mateuszb0k/humanoid-head/vision-module/documentation/training_details.pdf

### Vision Module - Technical Documentation

Mikoªaj Baran, Kewin Kisiel, Szymon Wójcik

March 2026

## Contents

1 Introduction | 3
2 Dataset Composition and Preprocessing | 3
3 Neural Network Architectures and Training | 4

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

## 1 Introduction

The primary objective of this project is the construction of a robotic head capable of two-way communication and emotional expression. The vision system's core responsibility is detecting user faces, extracting landmarks, and identifying aective states across seven categories: anger, sadness, fear, surprise, disgust, happiness, and neutral. The output data is utilized to personalize interactions via the speech synthesis subsystem.

## 2 Dataset Composition and Preprocessing

### 2.1 Data Sources

The training corpus was aggregated from diverse repositories to ensure high variance and reliability. Key sources included:

| Public Repositories: Aggregated versions of FER-2013, RAF-DB, and AectNet datasets.
| Synthetic Data: Images generated using the Gemini 2.0 model and expert-annotated bench- marks.
| Exp-W Dataset: An additional 19,290 images from the "Emotion Recognition in the Wild" dataset were integrated.
| Flux.1 Generation: 10,000 high-delity prompts were processed using the Flux.1 [dev] model to balance ethnic diversity.

### 2.2 Filtration and Cleaning Pipeline

To eliminate informational noise, the following algorithmic lters were applied:

| Deduplication (pHash): Perceptual hashing detected and removed 83,380 duplicated or near- duplicate images.
| Demographic Filtering: Images depicting infants (0-2 years) were removed using ViT-Age classiers.
| Artifact Removal: EasyOCR identied and rejected samples containing text overlays.
| Non-photorealistic Filtering: The CLIP model was used to exclude caricatures and 3D ren- ders.

After manual verication and annotation correction, the nal unied dataset reached 121,133 normalized images.

### 2.3 RGB Conversion and 224px Rescaling

While initial models utilized 96x96 grayscale images, standard DCNN architectures require 224x224 RGB inputs. To maintain consistency, a deep learning-based colorization algorithm using the CIE Lab color space was implemented.

| The L channel (brightness) was preserved from the original grayscale for sharpness.
| The a and b channels (chrominance) were estimated by a DCNN to reconstruct color information.

## 3 Neural Network Architectures and Training

### 3.1 Custom Models (Grayscale 96x96)

These models served as the project baseline to establish feature extraction capabilities.

3.1.1 rst_model

A classical CNN optimized for spatial feature extraction.

| Accuracy: 56.17%.
| Observation: Experienced rapid overtting starting at the 10th epoch.
3.1.2 | second_model and third_model

Improved architectures with deeper extraction blocks and aggressive dropout rates.

| second_model Accuracy: 71.04%.
| third_model Accuracy: 67.81%.

### 3.2 ConvNeXt Tiny Implementation Details

For both training runs of the ConvNeXt Tiny model, a consistent architectural conguration and two-phase training strategy were employed.

3.2.1 Common Model Conguration

The model was built using the ConvNeXtTiny base with weights='imagenet' and include_top=False. The custom classication head integrated:

| GlobalAveragePooling2D: To reduce spatial dimensions.
| BatchNormalization: For internal covariate shift stabilization.
| Dropout (0.4): To provide strong regularization.
| Dense Layers: One layer with 256 neurons (ReLU) and an output layer with 7 neurons (Soft- max).
3.2.2 | Two-Phase Training Strategy

Both runs followed a transfer learning workow:

1. Phase 1 (Warm-up): The base model was frozen (trainable = False). The classication
| head was trained for 5 epochs using the Adam optimizer with a learning rate of 1 × 10⁻³ and sparse_categorical_crossentropy loss.
2. Phase 2 (Fine-Tuning): The entire base model was unfrozen (trainable = True). The
| network was re-compiled with a signicantly lower learning rate of 1×10⁻⁵ to preserve ImageNet features while adapting to facial expressions.

### 3.3 ConvNeXt Tiny Training Runs Comparison

3.3.1 Run 1: Extended Fine-Tuning (20 Epochs Target)

In this iteration, the ne-tuning phase was scheduled for 20 epochs with an EarlyStopping callback monitoring val_accuracy (patience=5).

| Stability: The process was interrupted at epoch 15 due to a kernel crash caused by hardware memory exhaustion.
| Peak Metrics: Before the crash, the model achieved its highest recorded accuracy of 74.56% and a macro-precision of approximately 73.55%.
3.3.2 | Run 2: Stable Fine-Tuning (10 Epochs Target)

To ensure a complete training cycle and avoid further hardware failures, the second run was capped at 10 epochs for the ne-tuning phase.

| Stability: The training nished successfully, generating a nal .keras model le.
| Final Metrics: Achieved a validation accuracy of 73.60% and a macro-precision of 72.64%.

### 3.4 Xception (with Class Balancing)

The Xception architecture was evaluated using the same unied 121,133 image dataset, resized to 224x224 RGB. A dening characteristic of this specic model's training run was the utilization of computed class weights to counteract signicant dataset imbalance across the seven emotion categories.

3.4.1 Architecture and Conguration

The model utilized the Xception base pre-trained on ImageNet (include_top=False). The custom classication head was constructed as follows:

| GlobalAveragePooling2D: To atten spatial features.
| BatchNormalization: For internal covariate stabilization.
| Dropout (0.3): A lower dropout rate compared to the ConvNeXt run, tailored for this specic architecture.
| Dense Layers: One layer with 256 neurons (ReLU activation) and a nal 7-neuron output layer (Softmax).
3.4.2 | Training Strategy

The training process utilized computed class weights based on inverse class frequencies (loaded from class_weights.json) to heavily penalize misclassications of minority classes (like 'disgust' or 'fear'). The strategy involved two phases:

1. Phase 1 (Warm-up): The Xception base was frozen. The classication head was trained for 10
| epochs (interrupted early by callbacks after epoch 4) using the Adam optimizer with a learning rate of 1 × 10⁻³ and monitoring val_loss.
2. Phase 2 (Fine-Tuning): The entire Xception base was unfrozen (trainable=True). The
| network was re-compiled with a signicantly lower learning rate of 1 × 10⁻⁴ . Training was scheduled for an additional 20 epochs starting from epoch 4, but nished early after epoch 11 due to early stopping criteria.

3.4.3 Results and Performance

The Xception model achieved a nal validation accuracy of 64.92%. The confusion matrix reveals high accuracy for 'happiness' and 'neutral' expressions, but signicant challenges in dierentiating 'fear' and 'disgust', which were frequently misclassied as 'sadness' or 'anger', despite the application of class weights.


Figure 1: Training history: Xception Accuracy and Loss

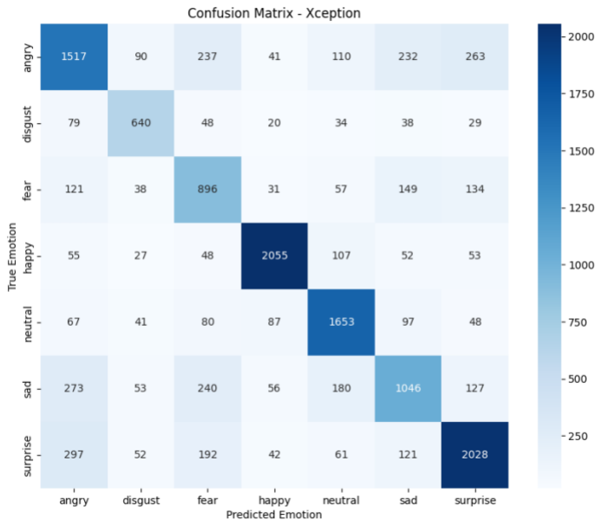
[picture p71: figure]

Figure 2: Normalized Confusion Matrix: Xception

### 3.5 ResNet50 (Initial Training Run)

The ResNet50 architecture was evaluated using the standardized 224x224 RGB dataset. This section details the initial training iteration before further optimizations.

3.5.1 Architecture and Conguration

The model utilized the ResNet50 base pre-trained on ImageNet (include_top=False). The custom classication head was constructed with:

| GlobalAveragePooling2D: To reduce spatial dimensions.
| BatchNormalization: For stabilizing the learning process.
| Dropout (0.4): Applied as a strong regularization measure.
| Dense Layers: One fully connected layer with 256 neurons (ReLU) and a nal 7-neuron output layer (Softmax).
3.5.2 | Training Strategy

The initial training run followed a standard two-phase transfer learning approach without explicit class weights:

1. Phase 1 (Warm-up): The base model was frozen. The classication head was trained for 5
| epochs using the Adam optimizer (LR = 1 × 10⁻³ ).

2. Phase 2 (Fine-Tuning): The entire base model was unfrozen, and the learning rate was reduced to 1 × 10⁻⁵
. The training was scheduled for 15 epochs with an EarlyStopping callback monitoring validation accuracy (patience of 5).

3.5.3 Results and Performance

In this rst training run, the ResNet50 model achieved a validation accuracy of 67.89% and a macro-precision of 66.21%.


Figure 3: Training history: ResNet50 (Run 1)


Figure 4: Confusion Matrix: ResNet50 (Run 1)

### 3.6 ResNet50 - Second Training Run

To surpass the performance of previous iterations, a second training run for the ResNet50 model was conducted using a rened two-stage transfer learning strategy. The model architecture was extended with a custom classication head: Global Average Pooling, Batch Normalization, a Dropout layer (0.4), and a Dense layer with 256 units using ReLU activation.
The training parameters and process were structured as follows:
| Phase 1 (Warm-up): 5 epochs with a frozen ResNet50 base, utilizing the Adam optimizer with a learning rate of 1 × 10⁻³ .
| Phase 2 (Fine-tuning): The base was unfrozen and trained for 10 epochs with a signicantly lower learning rate of 1 × 10⁻⁵ to perform subtle weight adjustments.
| Callbacks: EarlyStopping was implemented with a patience of 5 and, crucially, restore_best_weights=True.


Figure 5: Training and validation metrics for the ResNet50 second run. The dashed red line indicates the transition from warm-up to ne-tuning.

The learning curves (Fig. 5) show a successful convergence. A notable observation is the behavior during the nal epochs of ne-tuning: while the training loss continued to decrease, the validation loss showed a slight upward trend, indicating the onset of overtting. However, due to the restore_best_weights parameter, the training process eectively "rewound" the model to the state of epoch 11, where validation accuracy was maximized and loss was at its lowest.


Figure 6: Confusion matrix for the optimized ResNet50 model.

The nal model achieved a peak accuracy of 75.22% and a macro-precision of 73.36%. As shown in the confusion matrix (Fig. 6), the model excels at identifying happy and neutral expressions. Consistent with previous models, the primary confusion occurs between sad and neutral classes, which is expected given the visual similarity of these expressions in the dataset. This result represents the best performance achieved in the project thus far.

### 3.7 ResNet101 (Initial Training Run)

To investigate whether a deeper residual architecture would yield better feature extraction, the ResNet101 model was subjected to a similar initial training process.

3.7.1 Architecture and Conguration

The architecture closely mirrored the ResNet50 setup, utilizing the ResNet101 base (include_top=False), but with a slightly more aggressive regularization applied to the classication head:

| GlobalAveragePooling2D and BatchNormalization.
| Dropout (0.5): Increased to 0.5 to counteract the higher risk of overtting associated with a signicantly deeper network.
| Dense Layers: 256 neurons (ReLU) and 7 neurons (Softmax).
3.7.2 | Training Strategy

The two-phase training strategy was identical to the ResNet50 initial run:
1. Phase 1 (Warm-up): Base frozen, 5 epochs, Adam optimizer (LR = 1 × 10⁻³
| ).
2. Phase 2 (Fine-Tuning): Base unfrozen, 15 epochs, Adam optimizer (LR = 1 × 10⁻⁵
| ).

3.7.3 Results and Performance

The initial ne-tuning of ResNet101 resulted in a validation accuracy of 67.45% and a macro-precision of 65.88%. Notably, despite its increased depth and parameter count, this initial run did not outperform the shallower ResNet50 model, indicating that the extra layers may not provide an immediate advantage for this specic dataset without further tuning.


Figure 7: Training history: ResNet101 (Run 1)


Figure 8: Confusion Matrix: ResNet101 (Run 1)

### 3.8 ResNet101 - Second Training Run

Building upon the successful two-stage training strategy implemented for ResNet50, a parallel optimization was conducted for the deeper ResNet101 architecture. To accommodate the increased memory requirements (VRAM) of the 101-layer network, the batch size was reduced from 32 to 16. The custom classication head remained identical to the ResNet50 conguration to ensure an objective comparison. The training process utilized the proven sequential approach:

| Phase 1 (Warm-up): 5 epochs with a frozen base, using the Adam optimizer (1 × 10⁻³ ).
| Phase 2 (Fine-tuning): The entire network was unfrozen and trained for 10 epochs applying a heavily reduced learning rate (1 × 10⁻⁵ ).
| Callbacks: EarlyStopping congured with restore_best_weights=True (patience=5) and ModelCheckpoint to secure optimal weights.


Figure 9: Training and validation metrics for the ResNet101 second run. The deeper architecture benets signicantly from the two-stage ne-tuning approach.

The learning curves (Fig. 9) demonstrate a highly eective training cycle. The transition into ne-tuning initially yields steady improvements in both metrics. As the training progresses, a divergence between the training and validation loss emerges, signaling the onset of overtting as the high-capacity model begins memorizing the training set. Fortunately, the EarlyStopping mechanism successfully intervened, rewinding the weights to the exact epoch where validation accuracy peaked.


Figure 10: Confusion matrix for the optimized ResNet101 model, showing the highest overall performance.

The optimized ResNet101 achieved an outstanding nal accuracy of 77.28% and a macro-precision of 76.00%, establishing it as the absolute top-performing model in the entire study. The confusion matrix (Fig. 10) reveals robust classication across the board. While inherent dataset challenges remain (such as distinguishing between sad and neutral), the extra depth of ResNet101 allowed for more nuanced feature extraction, comfortably exceeding the project's baseline target of 75%.

### 3.9 ConvNextV2 - compare

We also compared the ConvNeXt V2 model variants: Atto (3.7M parameters), Pico (9.1M parameters), Tiny (28.6M parameters), Base (89M parameters), and Huge (660M parameters). The evaluations were conducted on an NVIDIA RTX 6000 Ada Generation GPU with 48GB of VRAM. The input images were provided in RGB format at a resolution of 224x224 pixels.

3.9.1 | Architecture adn conguration
| GlobalAveragePooling2D and LayerNormalization.
| Dropout (0.4): Set to 0.4 to counteract the risk of overtting associated with a signicantly deeper network.
| Dense Layers: 256 neurons (GELU) and 7 neurons (Softmax).
3.9.2 | Pre-training

Class weights were calculated for the dataset to mitigate the issue of an uneven number of images for individual emotions. During this phase, the entire base architecture of the ConvNeXt model was frozen, and only the newly added classication layers were trained. The learning rate was set to a constant value of 1e-3.

3.9.3 Fine-tuning

In this phase, the base model was unfrozen; however, to preserve the previously learned low-level image features, its initial layers ("stem", "patch", and the rst two convolutional blocks) were refrozen. Only the deeper layers of the base model and the classier were subjected to training. A variable learning rate was applied using the Cosine Decay with Restarts schedule (with an initial value of 1e-5).

3.9.4 | Results
| ConvNeXtV2 Huge: Macro Precision: 0.6236, Validation Accuracy: ≈0.656
| ConvNeXtV2 Base: Macro Precision: 0.5969, Validation Accuracy: ≈0.630
| ConvNeXtV2 Tiny: Macro Precision: 0.5635, Validation Accuracy: ≈0.597
| ConvNeXtV2 Atto: Macro Precision: 0.4841, Validation Accuracy: ≈0.517
| ConvNeXtV2 Pico: Macro Precision: 0.4197, Validation Accuracy: ≈0.405


Figure 11: Confusion matrix for the optimized ConvNextV2 Tiny model, showing the highest overall performance.


Figure 12: Training and validation metrics for the ConvNextV2 Tiny second run.

## 4 ConvNeXtV2 - Custom Dataset

We decided to compare the ConvNeXt V1 and V2 architectures. We chose ve model sizes for this evaluation: Atto (3.7M parameters), Pico (9.1M parameters), Tiny (28.6M parameters), Base (89M parameters), and Huge (660M parameters).

4.0.1 New Dataset

For this training, we compiled a custom dataset. It includes:

| 10,000 images generated with FLUX using prompts based on the scientic denition of each emotion.
| 10,000 generated images that do not conform to these scientic denitions (e.g., featuring slightly turned faces).
| 59,000 pictures of real humans sourced from the ExpW dataset and Viktor Modroczký's dataset (found on Kaggle; please refer to the technical documentation for details).

We decided to create a new dataset using generated images to improve model accuracy. Upon inspecting the original dataset, we discovered it contained numerous low-quality images (e.g., poorly visible or obscured faces).

4.0.2 | Architecture and Conguration
| Augmentation includes Random Flip, 15% rotation, 15% zoom-in, translations, as well as bright- ness and contrast adjustments.
| We normalized the pixel values to [-1, 1], which is necessary for ConvNeXtV2 models.

| ConvNeXtV2 models were initialized with ImageNet weights (for the Atto and Pico variants) and ImageNet-21k-ft1k weights (for the Tiny, Base, and Huge variants).
| Model Architecture:
| GlobalAveragePooling2D BatchNormalization Dense (512 neurons): With GELU activation function. Dropout (0.4) Dense (256 neurons): With GELU activation function. Dropout (0.2) Output Layer (Dense): 7 neurons with Softmax activation function for emotion classica- tion.
4.0.3 | Pre-training

In the rst phase, we focus on training the newly added classication layers, while the previously trained base layers remain frozen.

| All base layers frozen.
| Epochs: 10
| Learning Rate: Training begins with a 2-epoch warmup, after which the learning rate reaches a maximum value of 0.001, and then gradually decreases following a cosine decay schedule.
| Loss Function: Categorical Crossentropy.
| Class balancing was applied to compensate for the uneven number of samples across individual emotions.
4.0.4 | Fine-tuning

Fine-tuning consists of two phases where we progressively unfreeze specic layers.

Phase 1: Partial Fine-Tuning

| The last two deepest sections of the base model, responsible for analyzing high-level semantic image features, were unfrozen. The initial layers remained frozen.
| Epochs: 10
| The base Learning Rate was reduced to 0.00003 (3e-5).

Phase 2: Full Fine-Tuning

| All four main sections of the base model were unfrozen.
| The "stem" and "patch" layers were kept frozen, as they are responsible for basic shape and edge detection.
| Epochs: 15
| A low base Learning Rate of 0.00001 (1e-5) was applied.

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

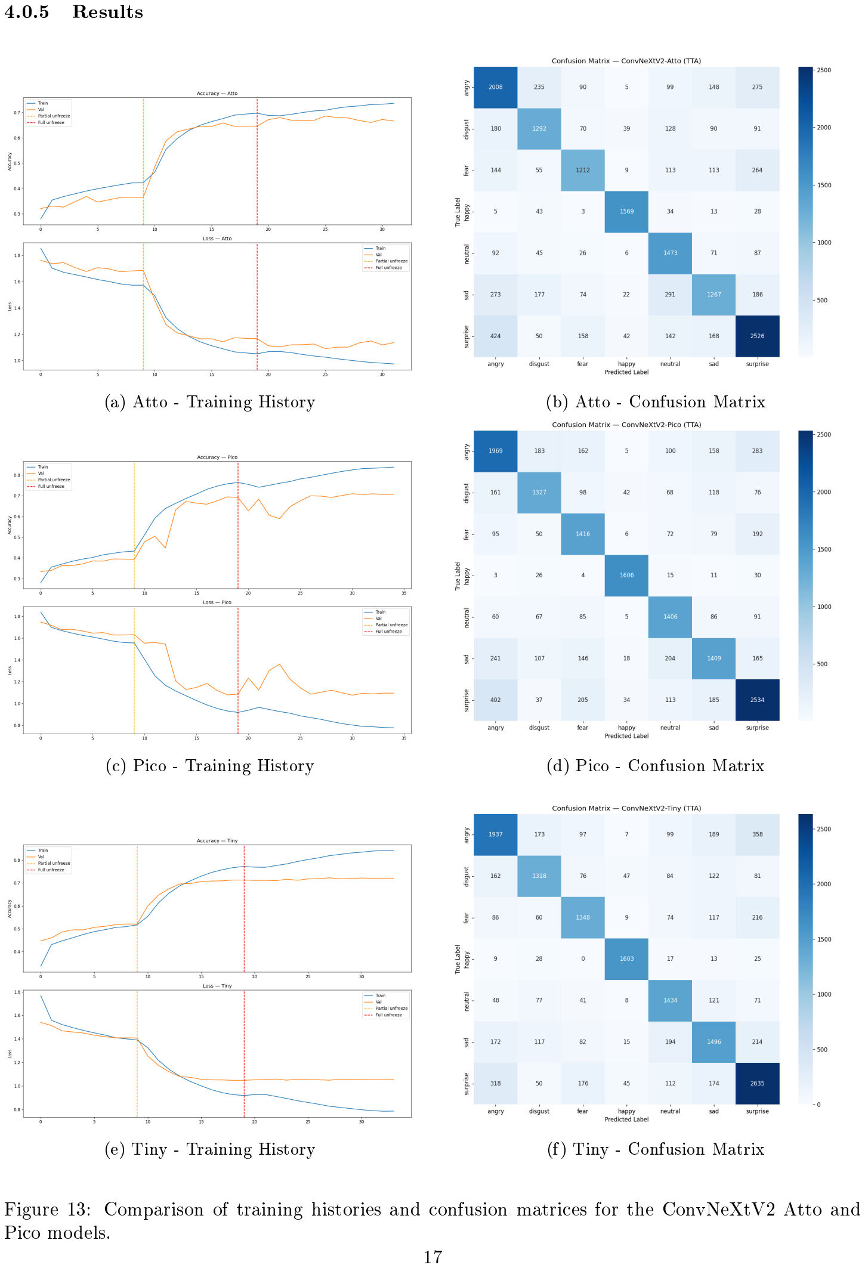
[picture p72: page 17]

4.0.5 | Results
(a) Atto - Training History | (b) Atto - Confusion Matrix
(c) Pico - Training History | (d) Pico - Confusion Matrix
(e) Tiny - Training History | (f) Tiny - Confusion Matrix

Figure 13: Comparison of training histories and confusion matrices for the ConvNeXtV2 Atto and Pico models.

## 5 Final Comparison and Benchmarking

The following table provides a comprehensive summary of the performance metrics achieved by all evaluated architectures. The models are ranked by their validation accuracy. This comparison highlights the transition from custom baseline models to state-of-the-art architectures using advanced ne-tuning techniques on the unied 121,133 image dataset.

Model | Accuracy | Macro-Precision
ResNet101 (Fine-tuned, Two-stage) ResNet50 (Fine-tuned, Two-stage) ConvNeXt Tiny (Run 1 - 15 epochs) ConvNeXt Tiny (Run 2 - 10 epochs) second_model (Custom) VGG19 VGG16 ResNet50 (Initial Training Run) third_model (Custom) ResNet101 (Initial Training Run) ConvNeXtV2 Huge Xception (with Class Balancing) InceptionV3 (with Class Balancing) ConvNeXtV2 Base ConvNeXtV2 Tiny rst_model (Custom) ConvNeXtV2 Atto ConvNeXtV2 Pico ConvNeXtV2 Tiny | 77.28% 75.22% 74.56% 73.60% 71.04% 70.07% 68.24% 67.89% 67.81% 67.45% 65.60% 64.92% 63.74% 63.00% 59.70% 56.17% 51.70% 40.50% 73.78% | 76.00% 73.36% 73.55% 72.64% 70.19% 69.47% 66.57% 66.21% 66.42% 65.88% 62.36% 63.81% 62.19% 59.69% 56.35% 54.03% 48.41% 41.97% 74.45%

Table 1: Final comparison of model performance metrics on the unied RGB dataset.

### 5.1 Performance Summary

Analysis of the nal benchmarks reveals that the optimized ResNet101 and ResNet50 architectures, trained using the two-stage ne-tuning approach, have become the superior choices for the vision module. Both models successfully exceeded the project's target accuracy of 75%, with ResNet101 reaching a peak of 77.28% and ResNet50 achieving 75.22%.
While the ConvNeXt Tiny architecture remained a very strong and modern contender (74.56%), the additional depth and rened training process of the ResNet family allowed for more precise feature extraction in the facial expression domain. The results also show that while custom models like second_model perform well for their size, they cannot match the generalization capabilities of deeper, ne-tuned residual networks. The application of class weights in other models like Xception provided better balance for minority classes, but the overall accuracy and reliability of ResNet101 make it the denitive leader of this comparison.

## 6 Conclusion

The development of the vision module successfully exceeded its initial goals. Through systematic experimentation and the implementation of an advanced two-stage training strategy, the ResNet101 architecture was selected as the primary vision engine, providing the most reliable results with an accuracy of 77.28%.
| The model demonstrates strong generalization and eectively handles the dicult task of distin-
guishing subtle emotional cues, even in historically problematic pairs like "sad" vs "neutral". This high level of performance ensures that the humanoid head can interact with users in a more natural and responsive manner. Future work will now focus on the deployment phase, specically optimizing and quantizing the ResNet101 model for real-time inference on the Raspberry Pi platform.
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
