mateuszb0k/humanoid-head/hardware-module/3Dmodel/base/cold_shoe_dimensions.webp

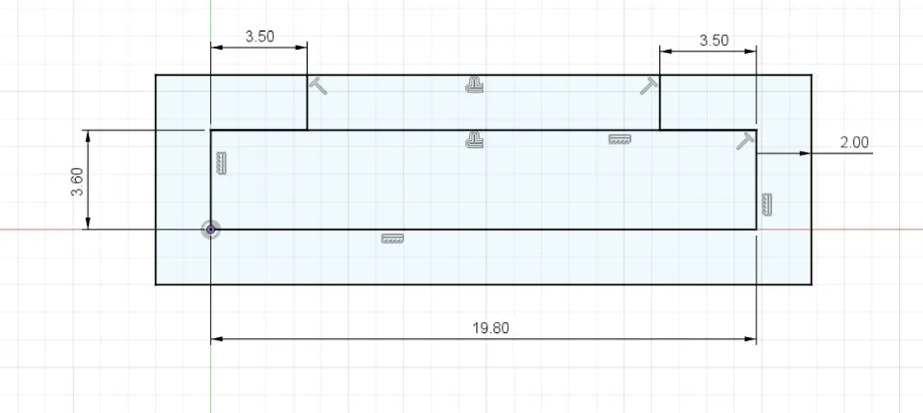
hardware-module/3Dmodel/base/cold_shoe_dimensions.webp
