mateuszb0k/humanoid-head/hardware-module/DescServos/viev_1.png

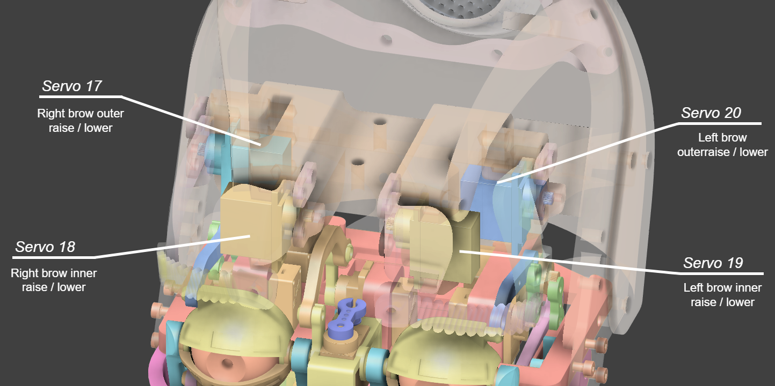
hardware-module/DescServos/viev_1.png
