mateuszb0k/humanoid-head/hardware-module/DescServos/viev_2.png

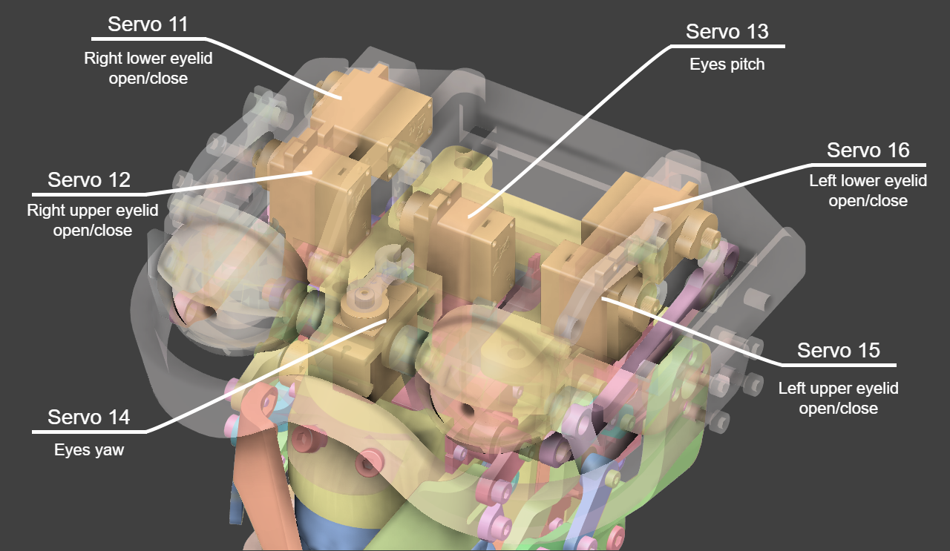
hardware-module/DescServos/viev_2.png
