mateuszb0k/humanoid-head/hardware-module/DescServos/viev_3.png

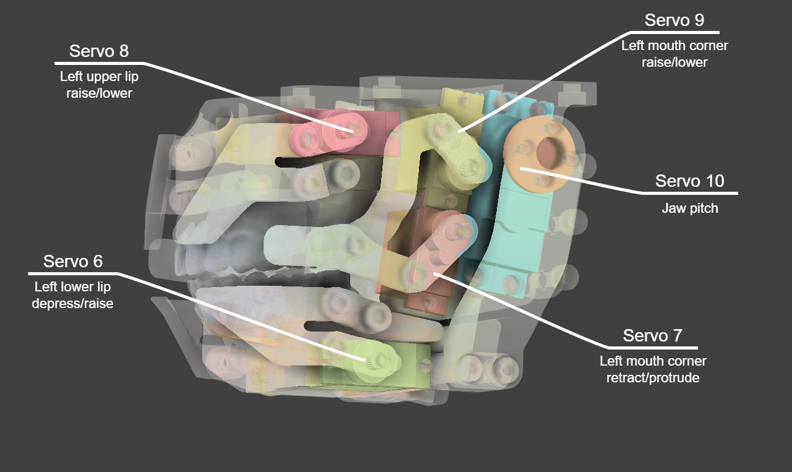
hardware-module/DescServos/viev_3.png
