mateuszb0k/humanoid-head/hardware-module/DescServos/viev_4.png

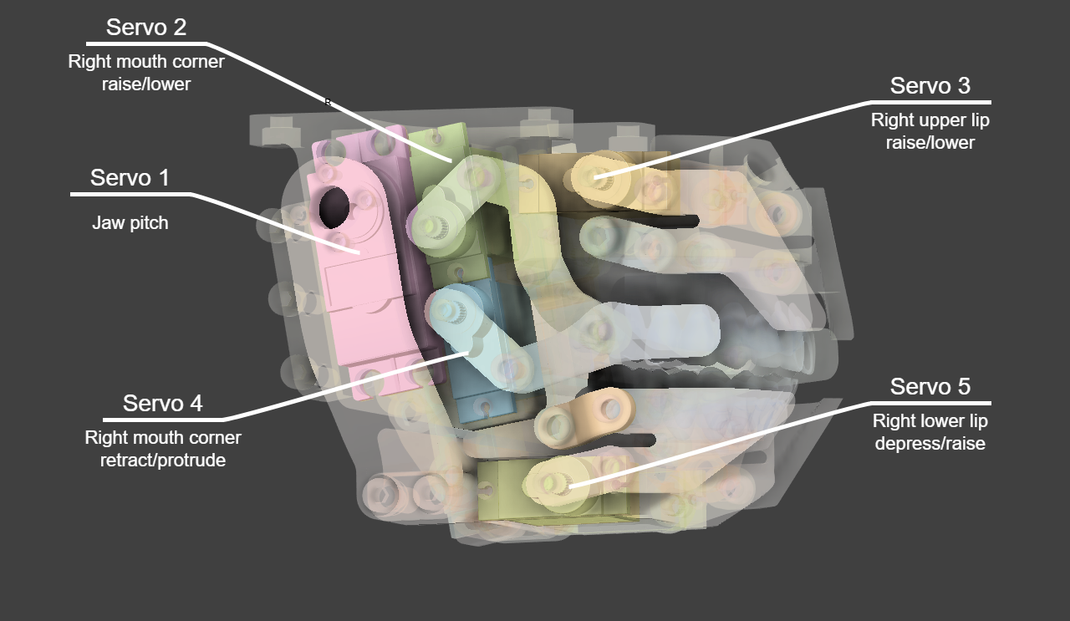
hardware-module/DescServos/viev_4.png
