mateuszb0k/humanoid-head/hardware-module/DescServos/viev_5.png

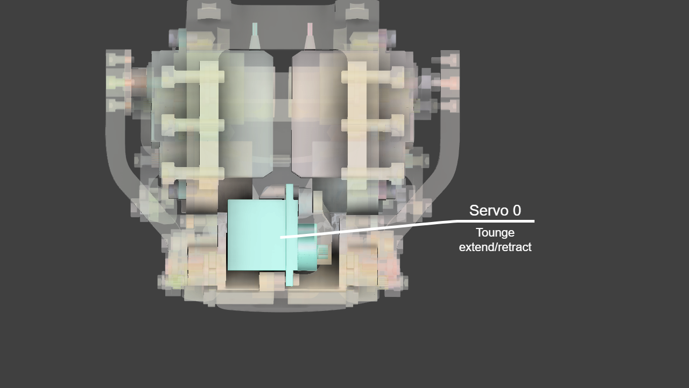
hardware-module/DescServos/viev_5.png
