mateuszb0k/humanoid-head/vision-module/images/download.png

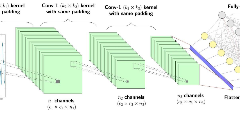
vision-module/images/download.png
