mateuszb0k/humanoid-head/hardware-module/3Dmodel/head stl/rampMount1.stl

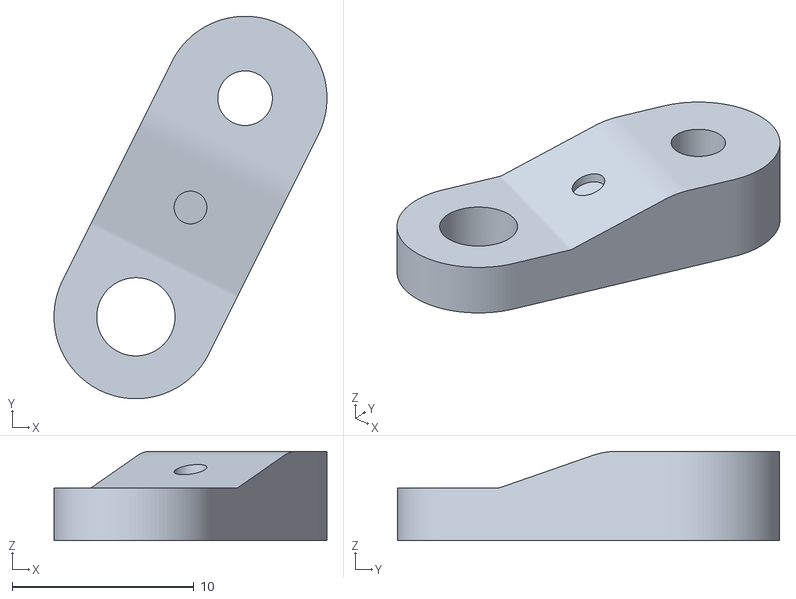
[picture p95: CAD file, 2026-03-23]
hardware-module/3Dmodel/head stl/rampMount1.stl
15.0 x 21.0 x 4.90
