mateuszb0k/humanoid-head/hardware-module/3Dmodel/head stl/forehead1right.stl

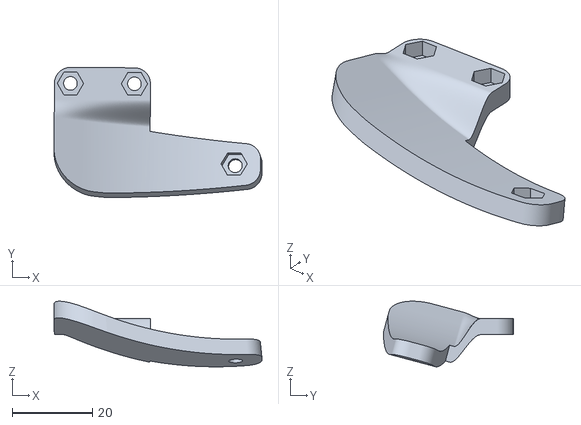
[picture p96: CAD file, 2026-03-23]
hardware-module/3Dmodel/head stl/forehead1right.stl
52.0 x 32.5 x 16.4
