mateuszb0k/humanoid-head/hardware-module/3Dmodel/head stl/baseConnector1.stl

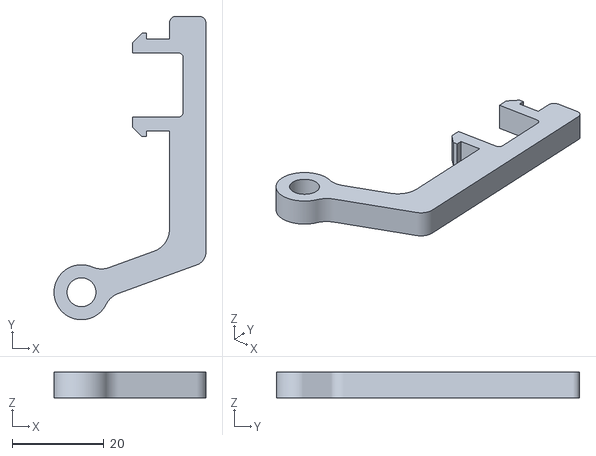
[picture p97: CAD file, 2026-03-23]
hardware-module/3Dmodel/head stl/baseConnector1.stl
33.2 x 66.3 x 5.60
