mateuszb0k/humanoid-head/hardware-module/3Dmodel/head stl/cheekConnector1b.stl

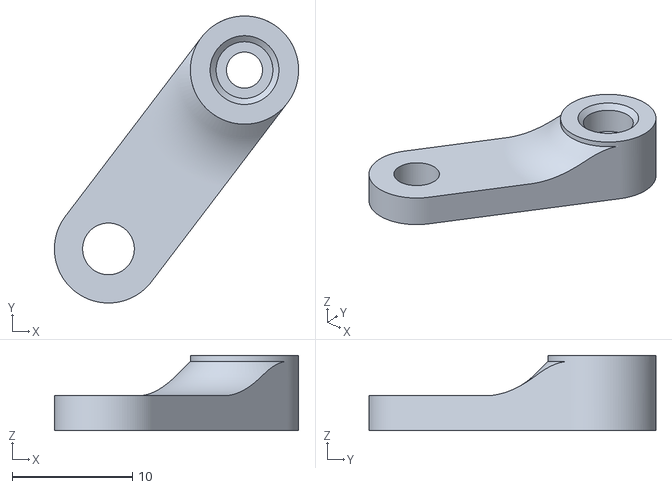
[picture p98: CAD file, 2026-03-23]
hardware-module/3Dmodel/head stl/cheekConnector1b.stl
20.3 x 23.9 x 6.25
