mateuszb0k/humanoid-head/hardware-module/3Dmodel/head stl/pad2.stl

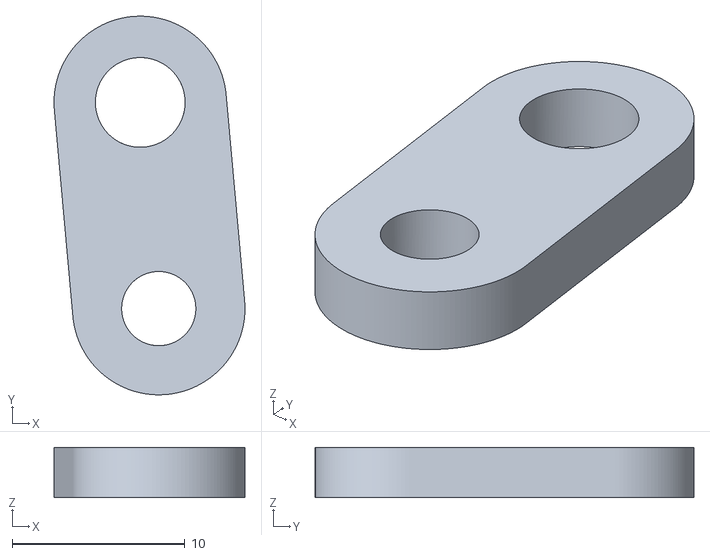
[picture p99: CAD file, 2026-03-23]
hardware-module/3Dmodel/head stl/pad2.stl
11.1 x 22.0 x 2.90
