mateuszb0k/humanoid-head/hardware-module/3Dmodel/head stl/baseConnector4.stl

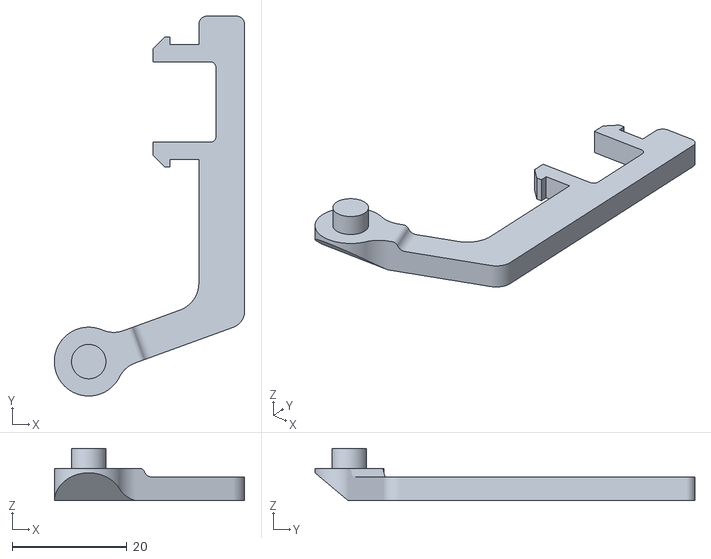
[picture p100: CAD file, 2026-03-23]
hardware-module/3Dmodel/head stl/baseConnector4.stl
33.2 x 66.3 x 9.10
