mateuszb0k/humanoid-head/hardware-module/3Dmodel/head stl/structure.stl

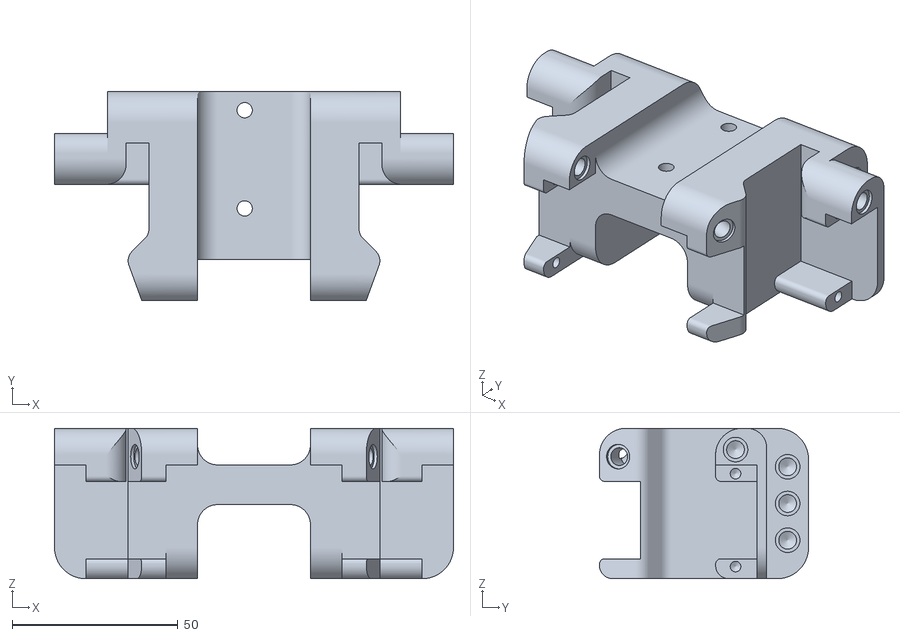
[picture p101: CAD file, 2026-03-23]
hardware-module/3Dmodel/head stl/structure.stl
120.2 x 63.0 x 45.3
