mateuszb0k/humanoid-head/hardware-module/3Dmodel/head stl/forehead2left.stl

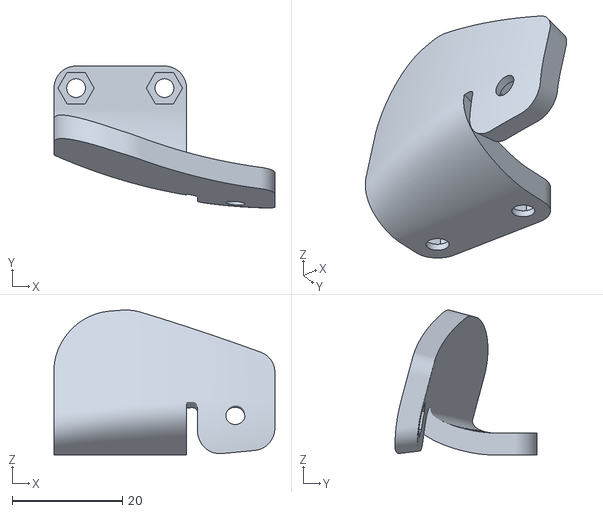
[picture p102: CAD file, 2026-03-23]
hardware-module/3Dmodel/head stl/forehead2left.stl
40.0 x 25.7 x 26.3
