mateuszb0k/humanoid-head/hardware-module/3Dmodel/head stl/baseClamp2.stl

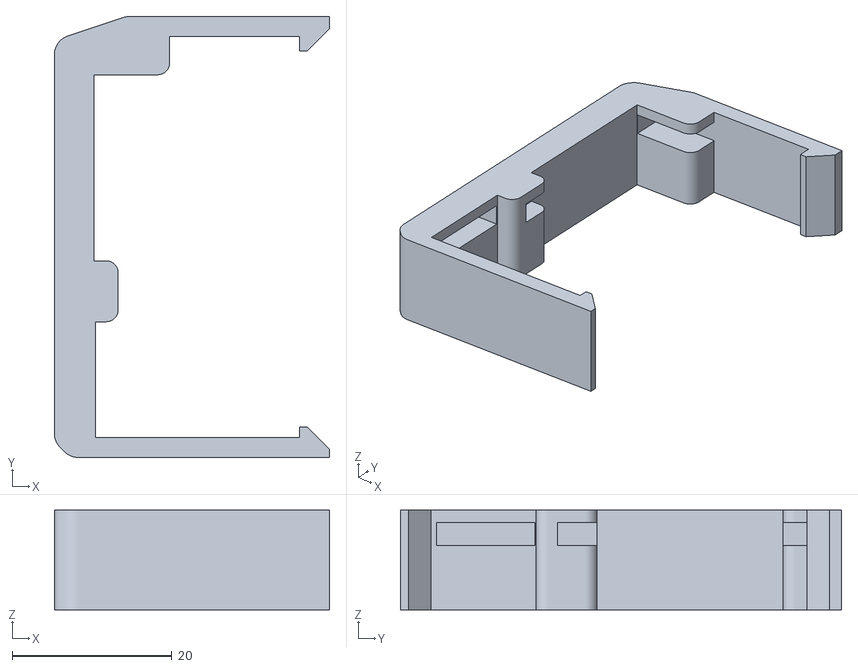
[picture p103: CAD file, 2026-03-23]
hardware-module/3Dmodel/head stl/baseClamp2.stl
34.5 x 55.2 x 12.5
