mateuszb0k/humanoid-head/hardware-module/3Dmodel/head stl/smallMount3.stl

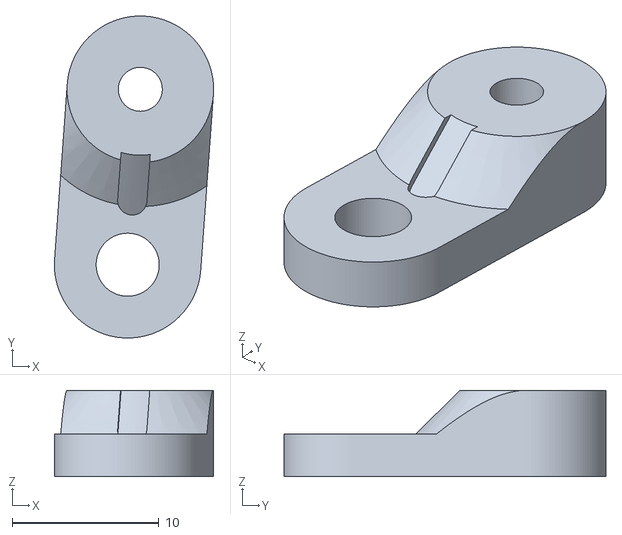
[picture p104: CAD file, 2026-03-23]
hardware-module/3Dmodel/head stl/smallMount3.stl
10.9 x 22.0 x 5.90
