mateuszb0k/humanoid-head/hardware-module/3Dmodel/head stl/topLidLever1.stl

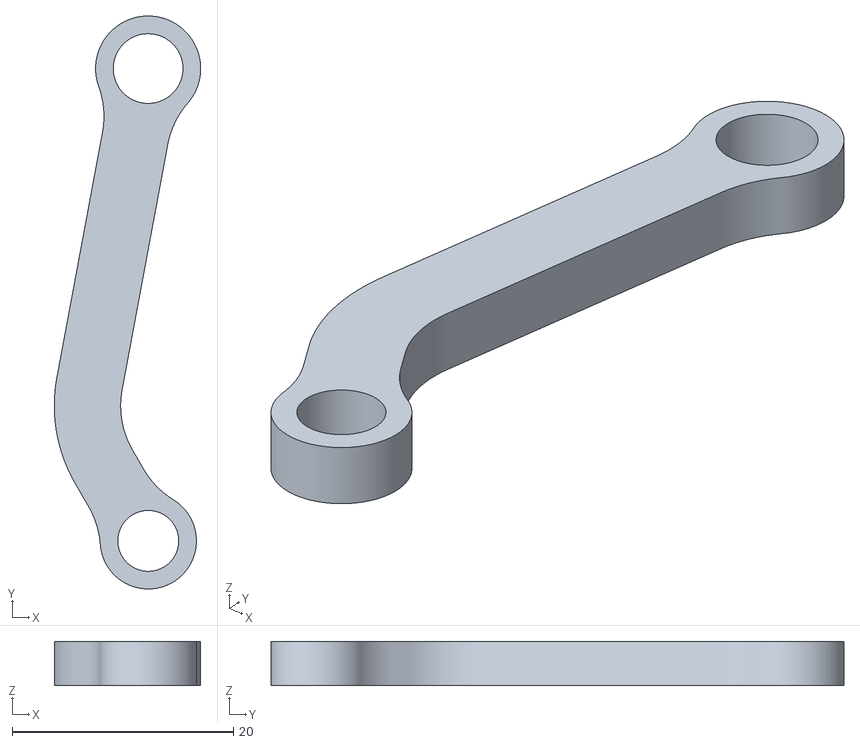
[picture p105: CAD file, 2026-03-23]
hardware-module/3Dmodel/head stl/topLidLever1.stl
13.2 x 51.8 x 4.00
