mateuszb0k/humanoid-head/hardware-module/3Dmodel/head stl/cheekBone.stl

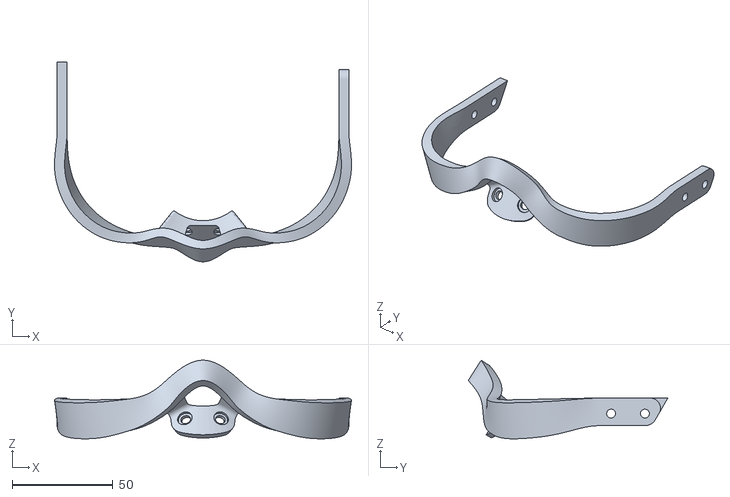
[picture p106: CAD file, 2026-03-23]
hardware-module/3Dmodel/head stl/cheekBone.stl
147.6 x 99.2 x 39.1
