mateuszb0k/humanoid-head/hardware-module/3Dmodel/head stl/smallMount4.stl

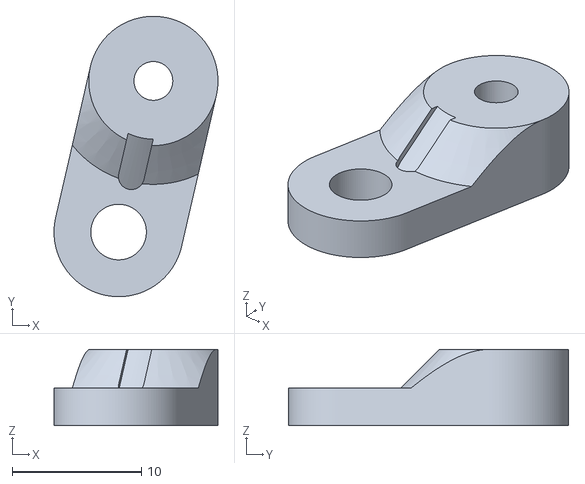
[picture p107: CAD file, 2026-03-23]
hardware-module/3Dmodel/head stl/smallMount4.stl
12.7 x 21.7 x 5.90
