mateuszb0k/humanoid-head/hardware-module/3Dmodel/head stl/topLidHorn1.stl

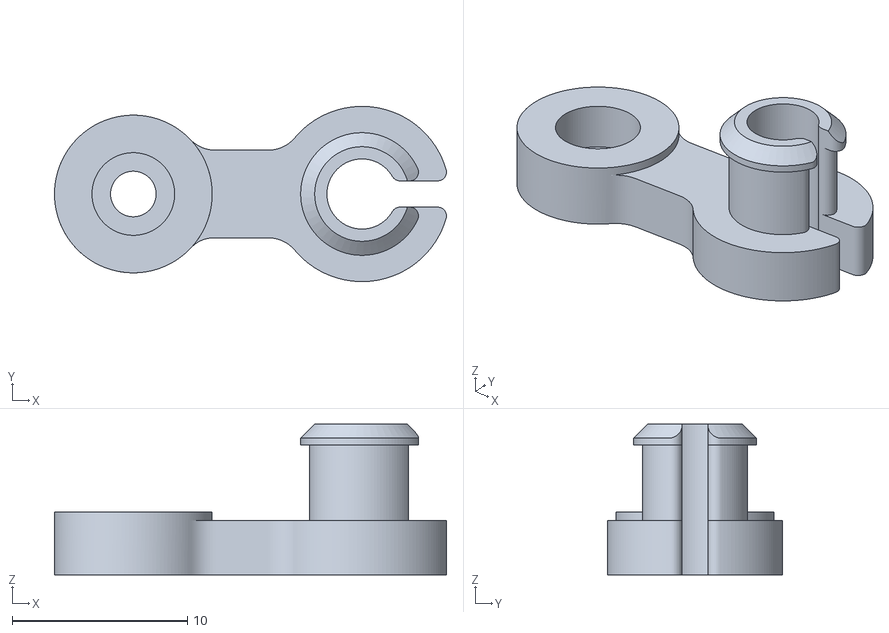
[picture p108: CAD file, 2026-03-23]
hardware-module/3Dmodel/head stl/topLidHorn1.stl
22.4 x 10.00 x 8.60
