mateuszb0k/humanoid-head/hardware-module/3Dmodel/head stl/link1a.stl

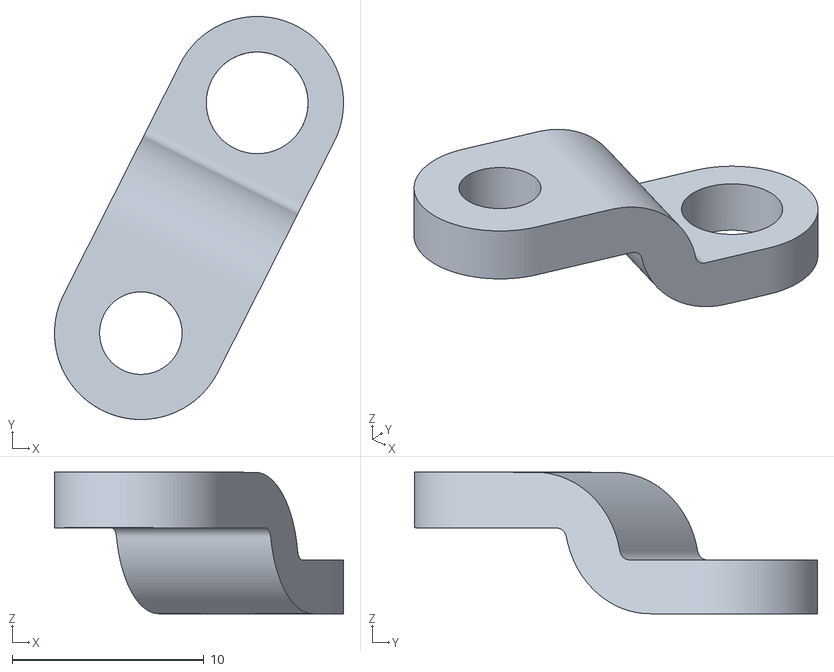
[picture p109: CAD file, 2026-03-23]
hardware-module/3Dmodel/head stl/link1a.stl
15.1 x 21.0 x 7.39
