mateuszb0k/humanoid-head/hardware-module/3Dmodel/head stl/bottomLidLever1.stl

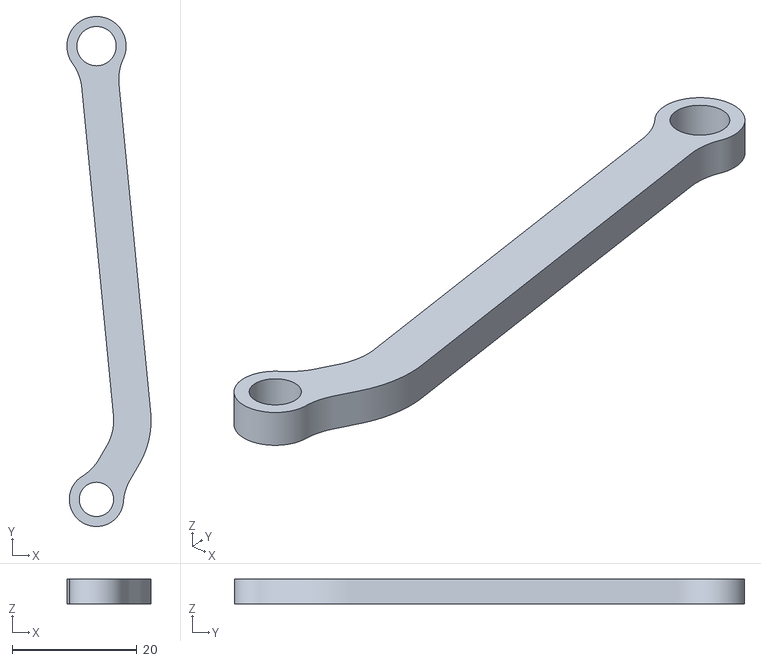
[picture p110: CAD file, 2026-03-23]
hardware-module/3Dmodel/head stl/bottomLidLever1.stl
13.5 x 81.8 x 4.00
