mateuszb0k/humanoid-head/hardware-module/3Dmodel/head stl/smallMount1.stl

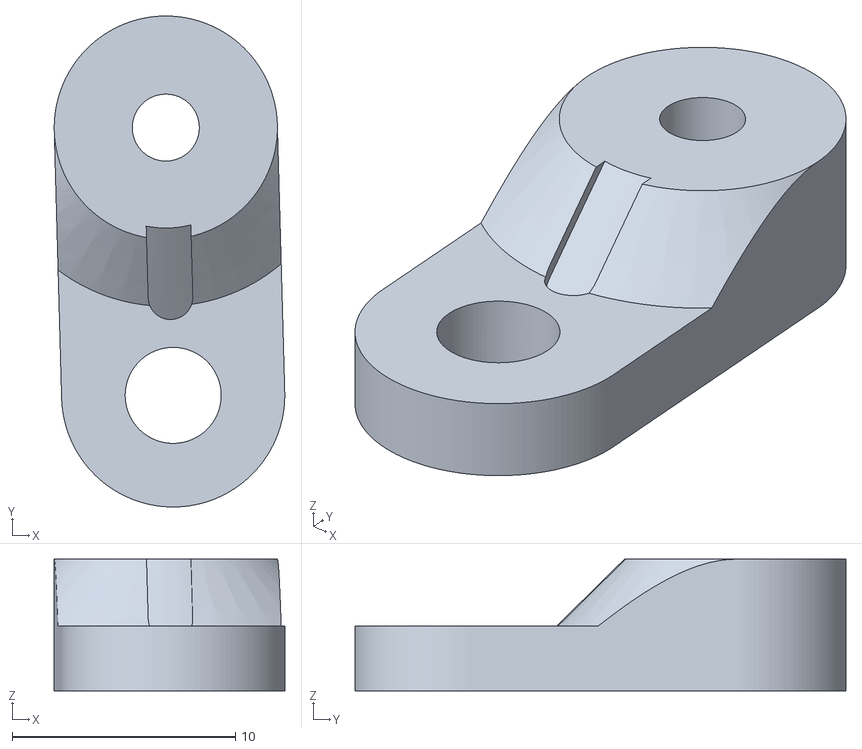
[picture p111: CAD file, 2026-03-23]
hardware-module/3Dmodel/head stl/smallMount1.stl
10.3 x 22.0 x 5.90
