mateuszb0k/humanoid-head/hardware-module/3Dmodel/head stl/skullFrame.stl

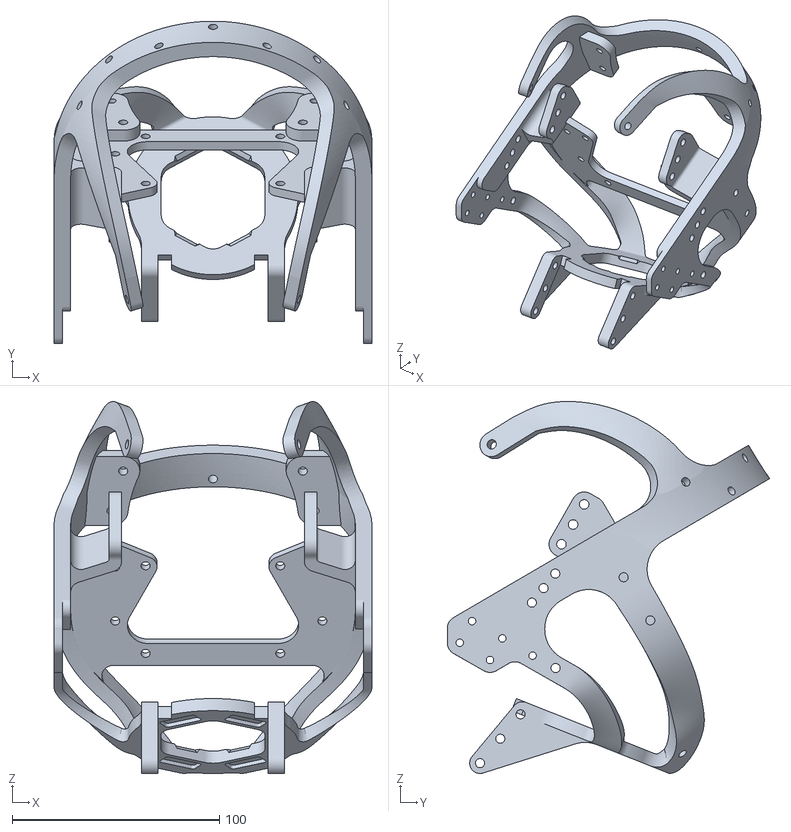
[picture p112: CAD file, 2026-03-23]
hardware-module/3Dmodel/head stl/skullFrame.stl
153.4 x 155.7 x 179.6
