mateuszb0k/humanoid-head/hardware-module/3Dmodel/head stl/tongueConnector1.stl

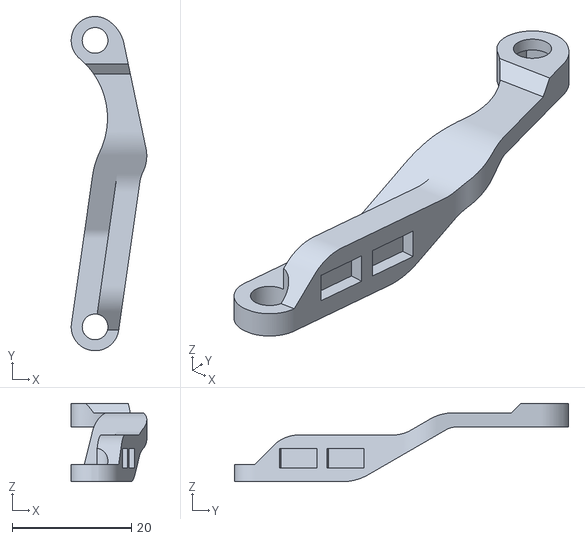
[picture p113: CAD file, 2026-03-23]
hardware-module/3Dmodel/head stl/tongueConnector1.stl
12.7 x 56.0 x 13.2
