mateuszb0k/humanoid-head/hardware-module/3Dmodel/head stl/lid1.stl

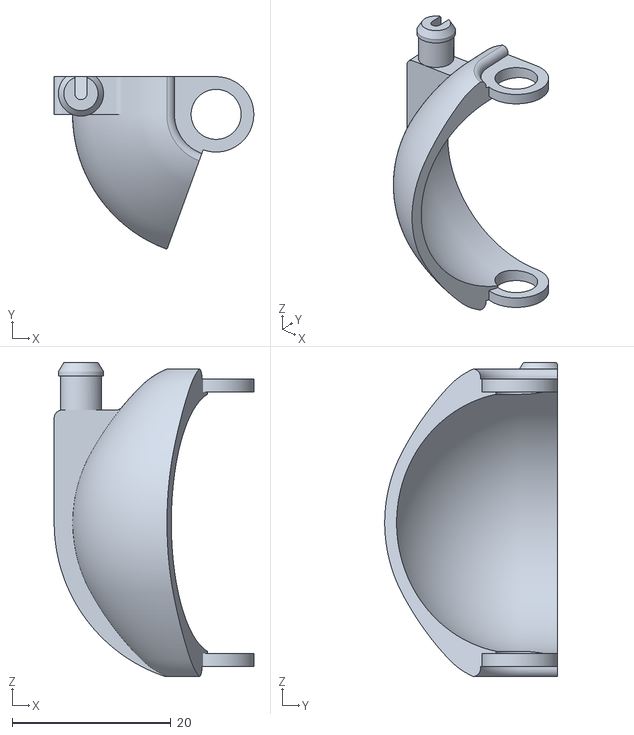
[picture p114: CAD file, 2026-03-23]
hardware-module/3Dmodel/head stl/lid1.stl
25.2 x 21.8 x 39.6
