mateuszb0k/humanoid-head/hardware-module/3Dmodel/head stl/link3d.stl

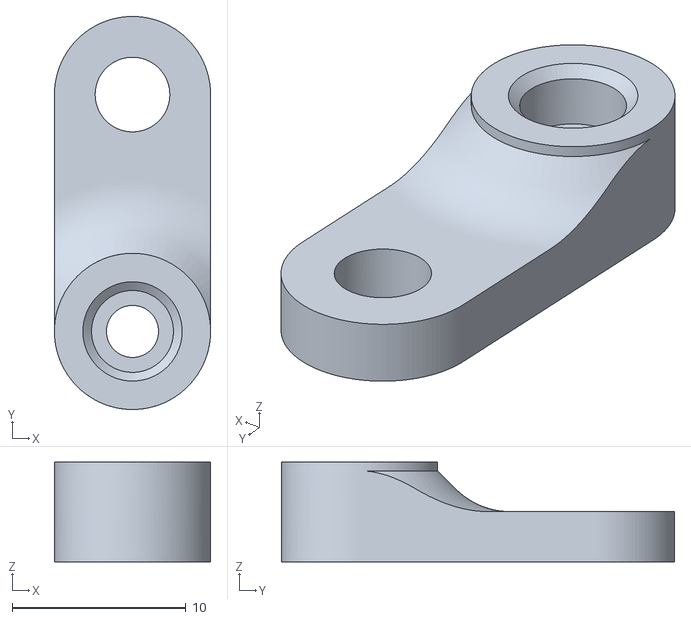
[picture p115: CAD file, 2026-03-23]
hardware-module/3Dmodel/head stl/link3d.stl
9.00 x 22.6 x 5.75
