mateuszb0k/humanoid-head/hardware-module/3Dmodel/head stl/braw1.stl

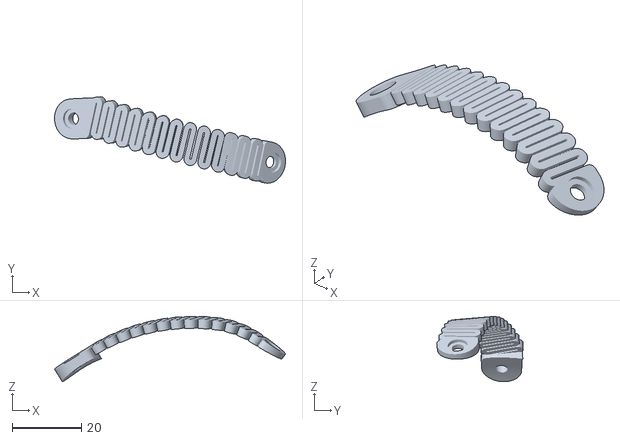
[picture p116: CAD file, 2026-03-23]
hardware-module/3Dmodel/head stl/braw1.stl
66.9 x 25.1 x 18.9
