mateuszb0k/humanoid-head/hardware-module/3Dmodel/head stl/sMountRight.stl

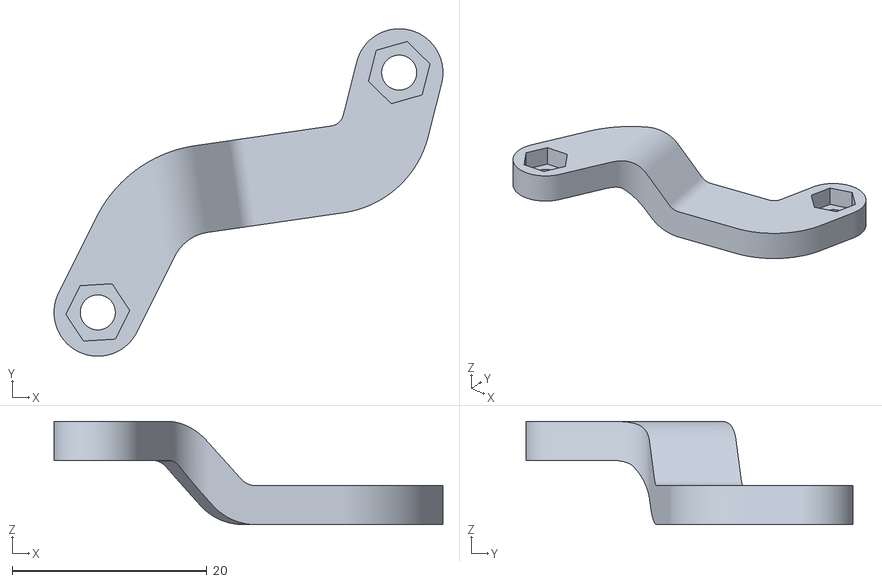
[picture p117: CAD file, 2026-03-23]
hardware-module/3Dmodel/head stl/sMountRight.stl
40.0 x 33.6 x 10.6
