mateuszb0k/humanoid-head/hardware-module/3Dmodel/head stl/tongueConnector2.stl

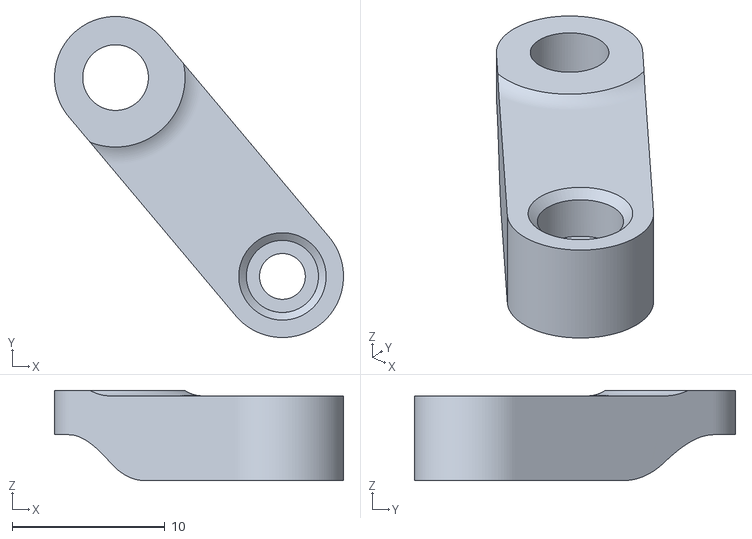
[picture p118: CAD file, 2026-03-23]
hardware-module/3Dmodel/head stl/tongueConnector2.stl
18.9 x 21.0 x 5.90
