mateuszb0k/humanoid-head/hardware-module/3Dmodel/head stl/jawConnector.stl

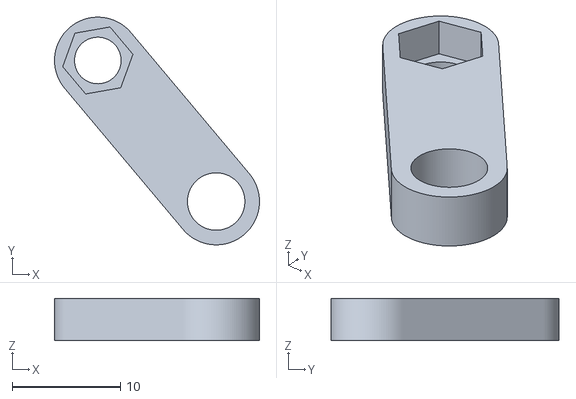
[picture p119: CAD file, 2026-03-23]
hardware-module/3Dmodel/head stl/jawConnector.stl
18.9 x 21.0 x 3.90
