mateuszb0k/humanoid-head/hardware-module/3Dmodel/head stl/jawBase.stl

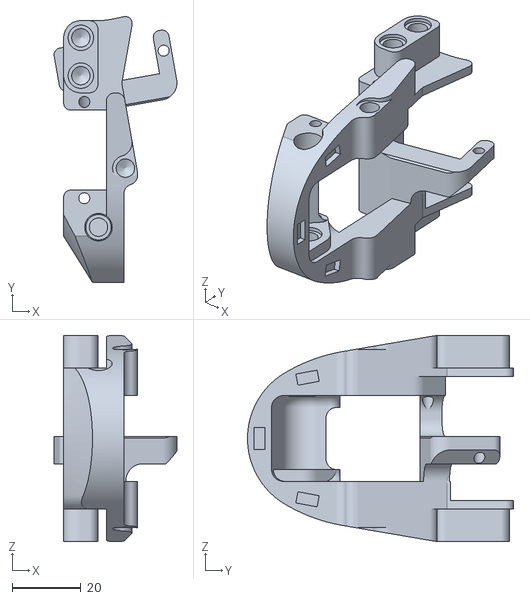
[picture p120: CAD file, 2026-03-23]
hardware-module/3Dmodel/head stl/jawBase.stl
35.7 x 77.4 x 60.0
