mateuszb0k/humanoid-head/hardware-module/3Dmodel/head stl/lowerLipLeft.stl

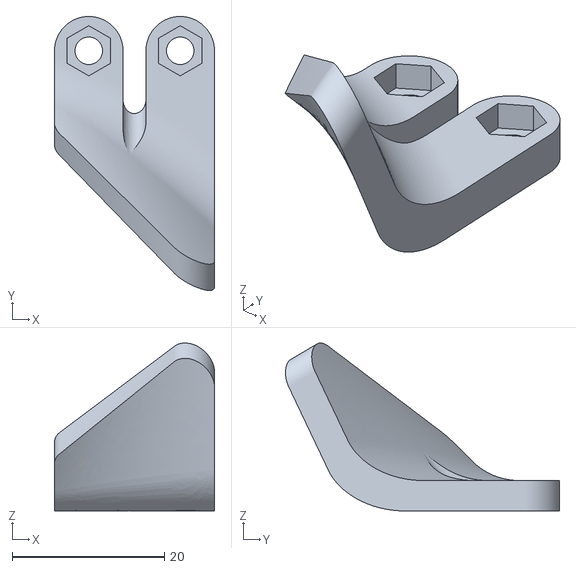
[picture p121: CAD file, 2026-03-23]
hardware-module/3Dmodel/head stl/lowerLipLeft.stl
21.0 x 36.0 x 22.0
