mateuszb0k/humanoid-head/hardware-module/3Dmodel/head stl/verticalHorn.stl

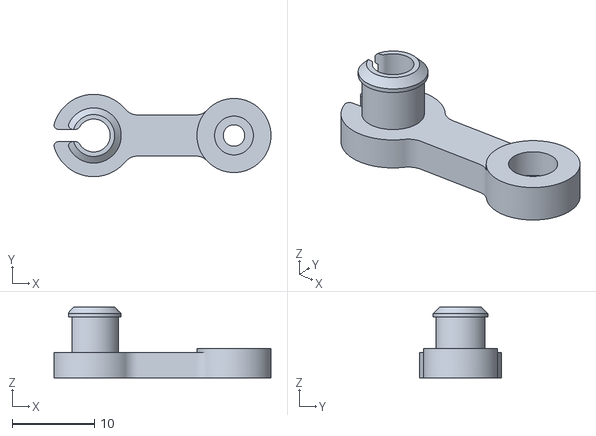
[picture p122: CAD file, 2026-03-23]
hardware-module/3Dmodel/head stl/verticalHorn.stl
26.4 x 10.00 x 8.60
