mateuszb0k/humanoid-head/hardware-module/3Dmodel/head stl/eyes.stl

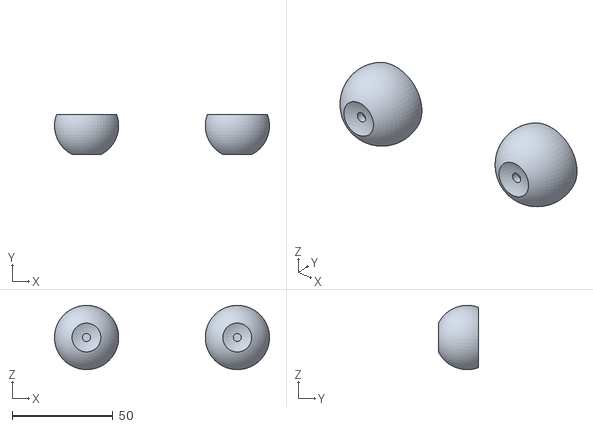
[picture p123: CAD file, 2026-03-23]
hardware-module/3Dmodel/head stl/eyes.stl
106.9 x 20.0 x 32.0
