mateuszb0k/humanoid-head/hardware-module/3Dmodel/head stl/forehead1left.stl

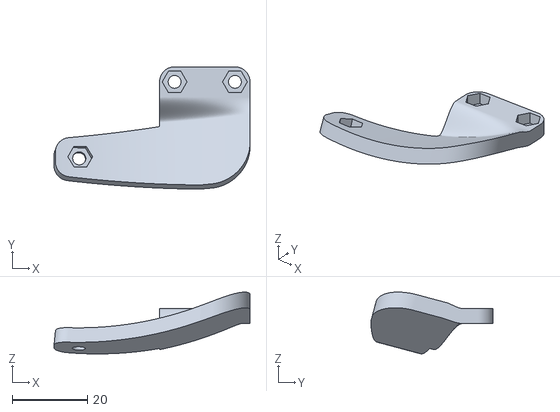
[picture p124: CAD file, 2026-03-23]
hardware-module/3Dmodel/head stl/forehead1left.stl
52.0 x 32.5 x 16.4
