mateuszb0k/humanoid-head/hardware-module/3Dmodel/head stl/eyeCorePivotHolder.stl

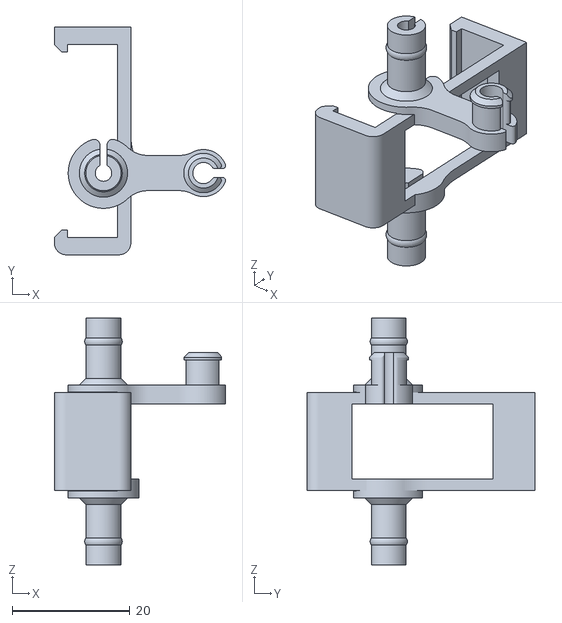
[picture p125: CAD file, 2026-03-23]
hardware-module/3Dmodel/head stl/eyeCorePivotHolder.stl
29.1 x 38.7 x 42.0
