mateuszb0k/humanoid-head/hardware-module/3Dmodel/head stl/tongue.stl

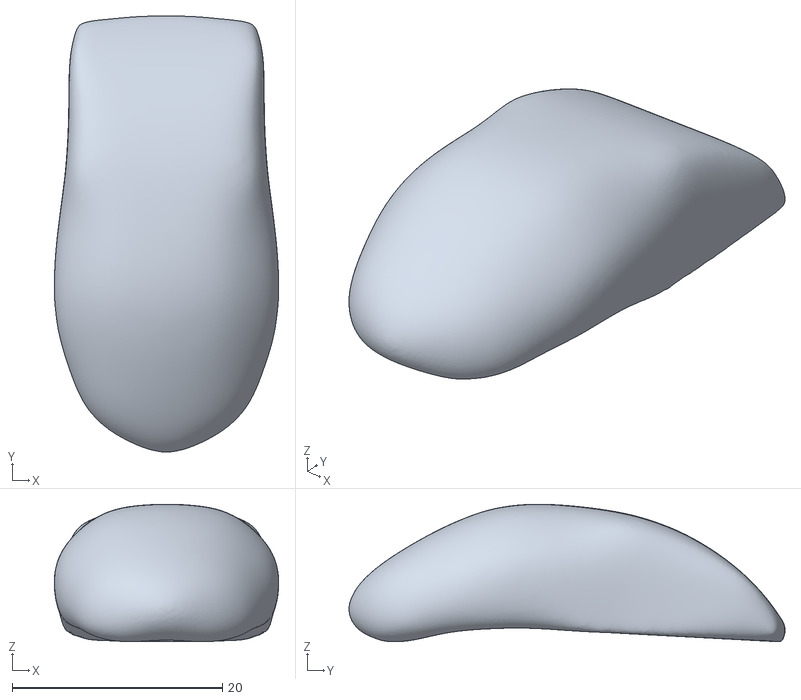
[picture p126: CAD file, 2026-03-23]
hardware-module/3Dmodel/head stl/tongue.stl
21.4 x 41.5 x 13.1
