mateuszb0k/humanoid-head/hardware-module/3Dmodel/head stl/teethDown.stl

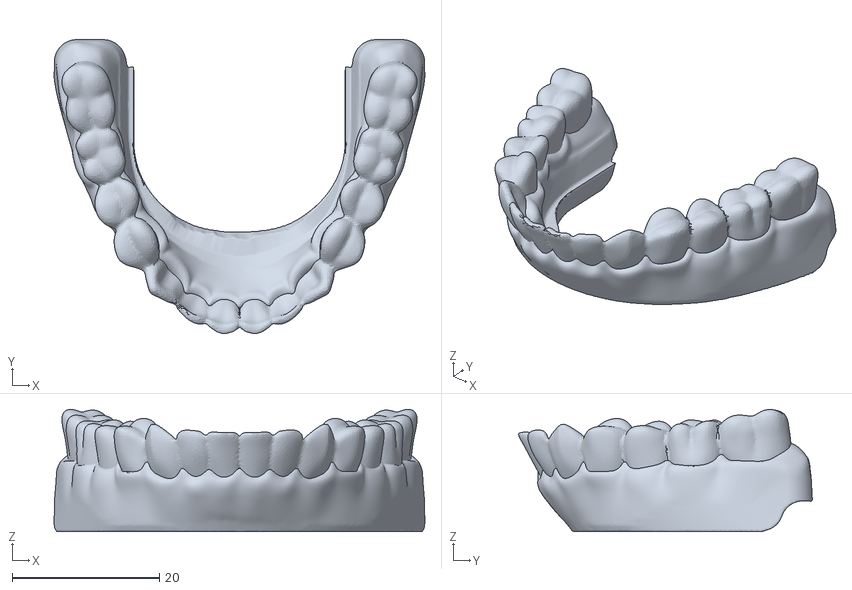
[picture p127: CAD file, 2026-03-23]
hardware-module/3Dmodel/head stl/teethDown.stl
50.3 x 39.8 x 16.6
