mateuszb0k/humanoid-head/hardware-module/3Dmodel/head stl/trippleLink.stl

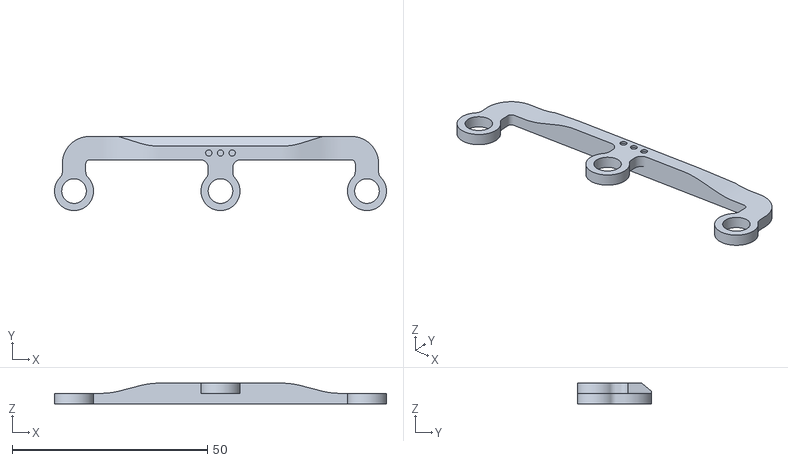
[picture p128: CAD file, 2026-03-23]
hardware-module/3Dmodel/head stl/trippleLink.stl
85.0 x 19.0 x 5.30
