mateuszb0k/humanoid-head/hardware-module/3Dmodel/head stl/cheekConnector1a.stl

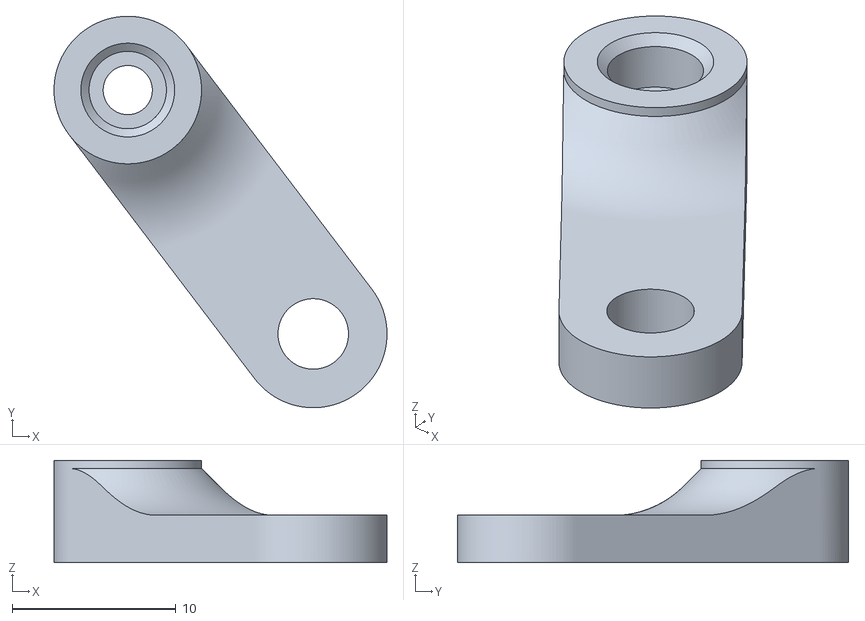
[picture p129: CAD file, 2026-03-23]
hardware-module/3Dmodel/head stl/cheekConnector1a.stl
20.3 x 23.9 x 6.25
