mateuszb0k/humanoid-head/hardware-module/3Dmodel/head stl/eyeAdaptor2.stl

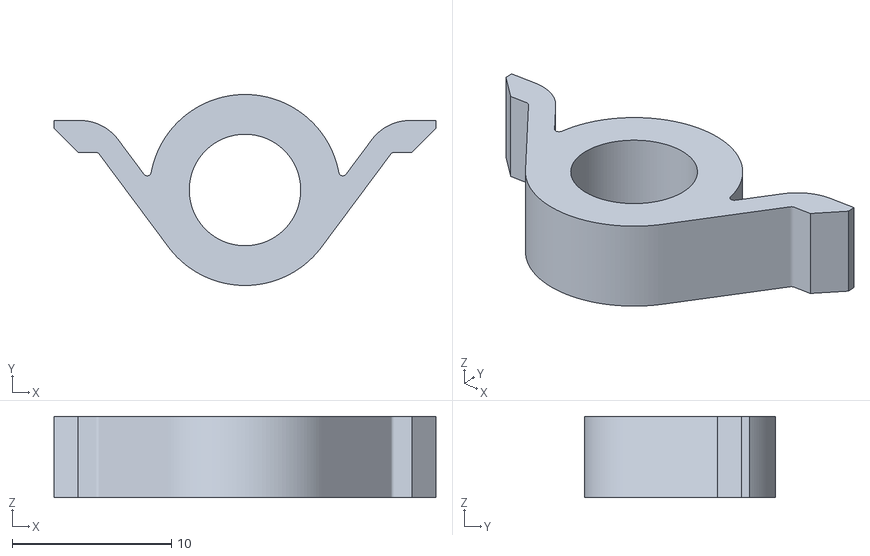
[picture p130: CAD file, 2026-03-23]
hardware-module/3Dmodel/head stl/eyeAdaptor2.stl
24.0 x 12.0 x 5.10
