mateuszb0k/humanoid-head/hardware-module/3Dmodel/head stl/teethUp.stl

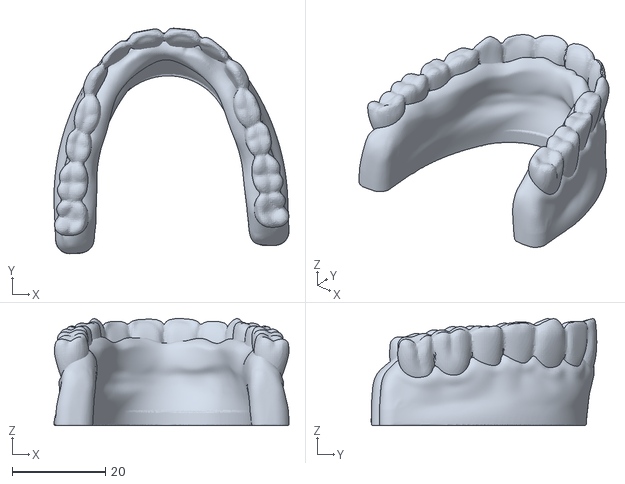
[picture p131: CAD file, 2026-03-23]
hardware-module/3Dmodel/head stl/teethUp.stl
50.3 x 48.2 x 22.9
