mateuszb0k/humanoid-head/hardware-module/3Dmodel/head stl/mount1Left.stl

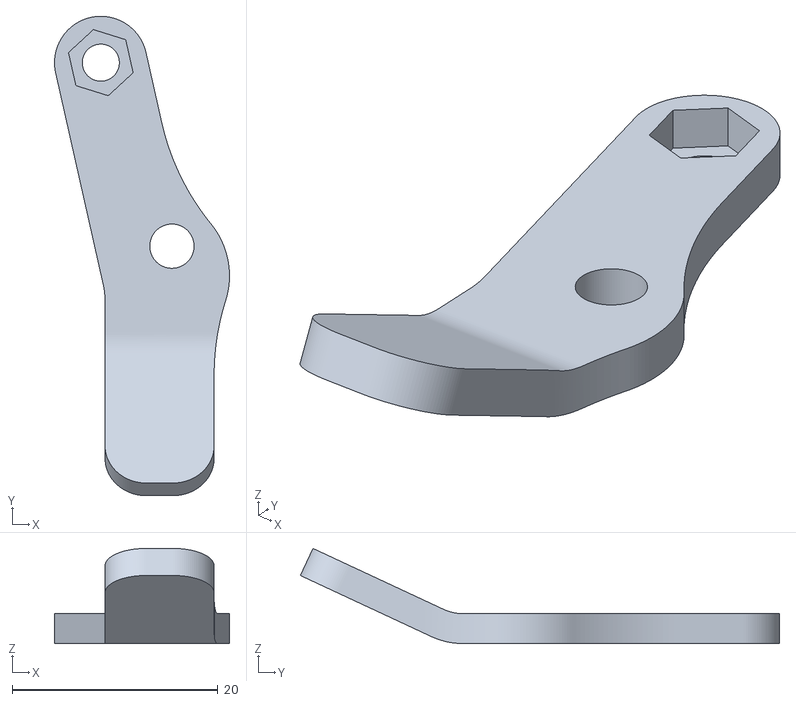
[picture p132: CAD file, 2026-03-23]
hardware-module/3Dmodel/head stl/mount1Left.stl
17.0 x 46.6 x 9.24
