mateuszb0k/humanoid-head/hardware-module/3Dmodel/head stl/link3b.stl

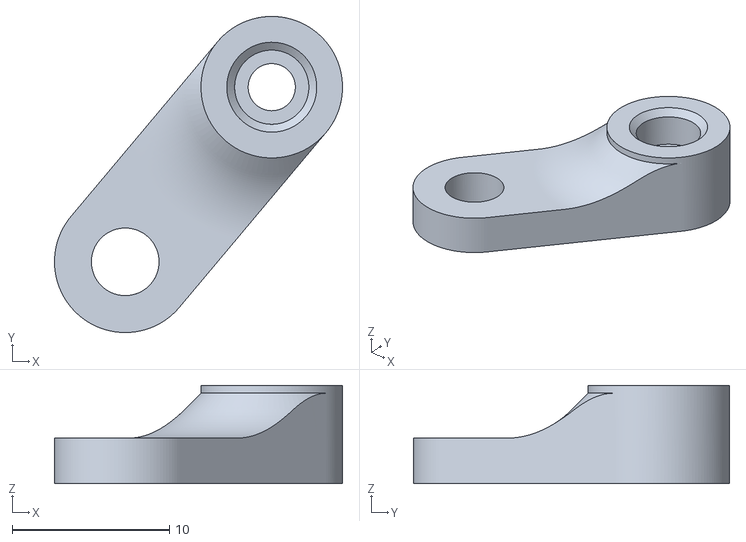
[picture p133: CAD file, 2026-03-23]
hardware-module/3Dmodel/head stl/link3b.stl
18.3 x 20.1 x 6.25
