mateuszb0k/humanoid-head/hardware-module/3Dmodel/head stl/fanBracket.stl

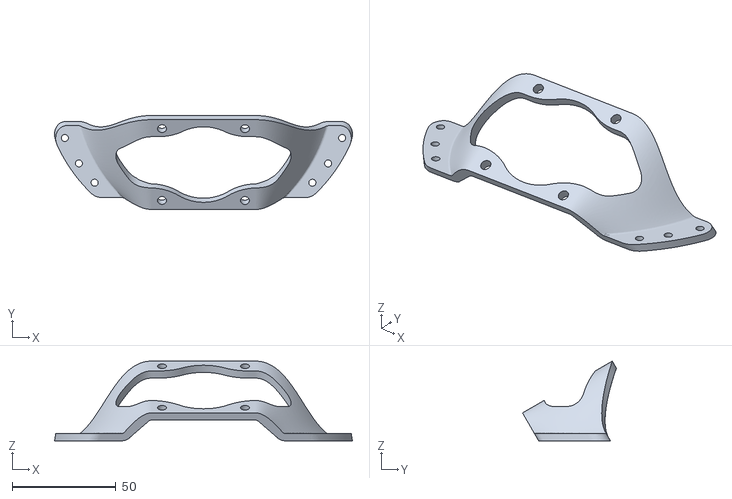
[picture p134: CAD file, 2026-03-23]
hardware-module/3Dmodel/head stl/fanBracket.stl
143.7 x 45.3 x 38.5
