mateuszb0k/humanoid-head/hardware-module/3Dmodel/head stl/link3c.stl

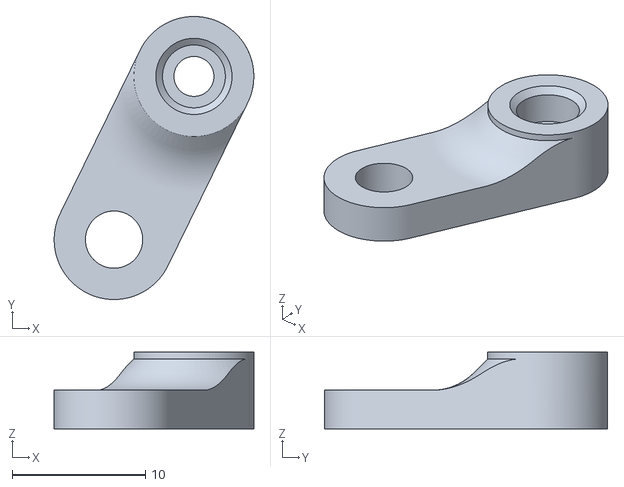
[picture p135: CAD file, 2026-03-23]
hardware-module/3Dmodel/head stl/link3c.stl
15.0 x 21.3 x 5.75
