mateuszb0k/humanoid-head/hardware-module/3Dmodel/head stl/rearPlate.stl

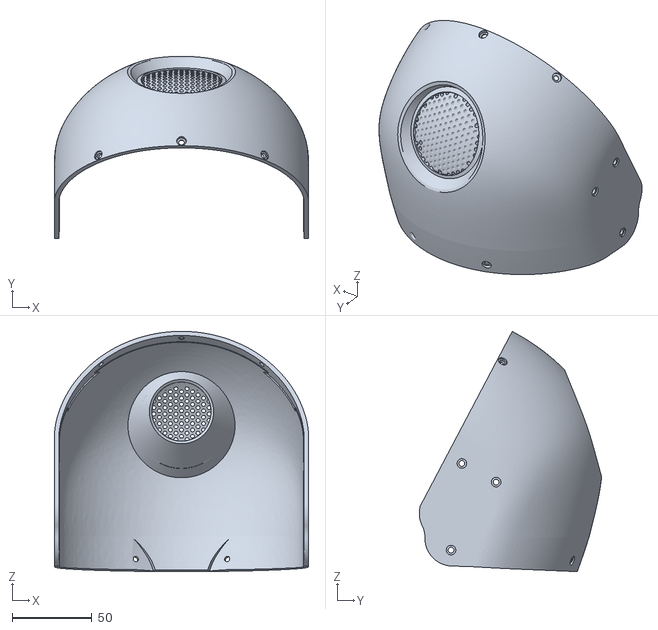
[picture p136: CAD file, 2026-03-23]
hardware-module/3Dmodel/head stl/rearPlate.stl
159.4 x 114.5 x 150.8
