mateuszb0k/humanoid-head/hardware-module/3Dmodel/head stl/base.stl

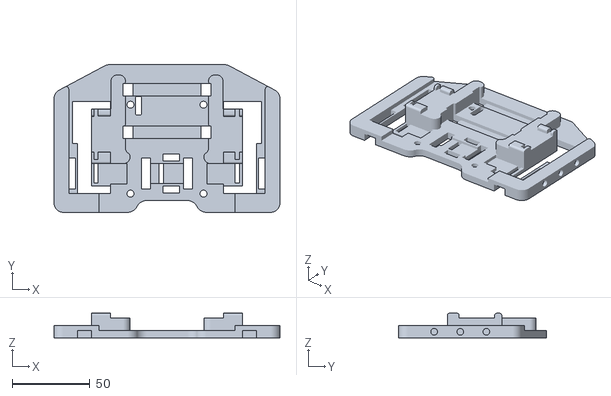
[picture p137: CAD file, 2026-03-23]
hardware-module/3Dmodel/head stl/base.stl
145.4 x 95.0 x 15.9
