mateuszb0k/humanoid-head/hardware-module/3Dmodel/head stl/frontPlate.stl

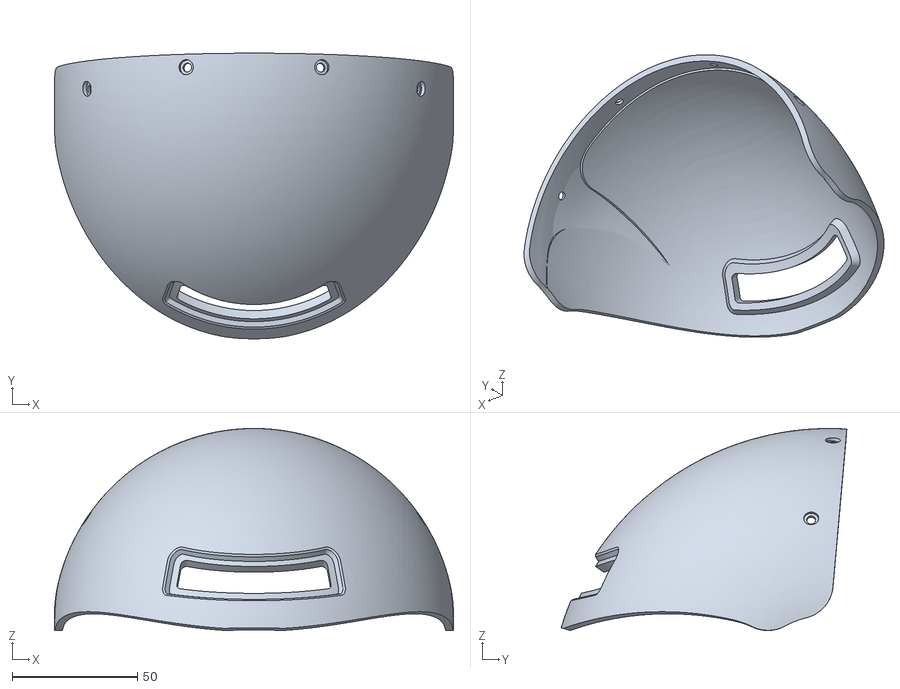
[picture p138: CAD file, 2026-03-23]
hardware-module/3Dmodel/head stl/frontPlate.stl
159.4 x 114.1 x 80.7
