mateuszb0k/humanoid-head/hardware-module/3Dmodel/head stl/baseClamp1.stl

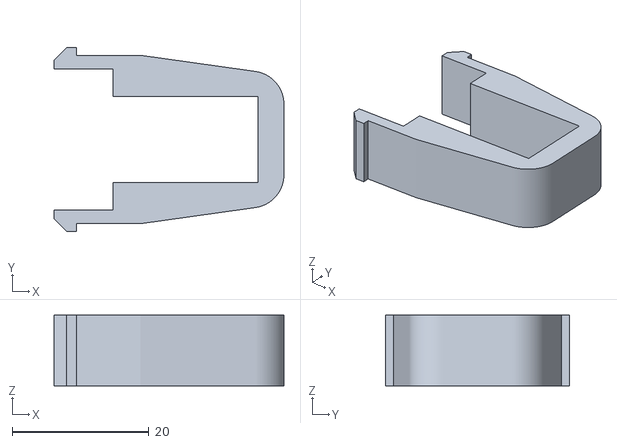
[picture p139: CAD file, 2026-03-23]
hardware-module/3Dmodel/head stl/baseClamp1.stl
33.6 x 26.8 x 10.3
