mateuszb0k/humanoid-head/hardware-module/3Dmodel/Photos/failure2_2.jpg

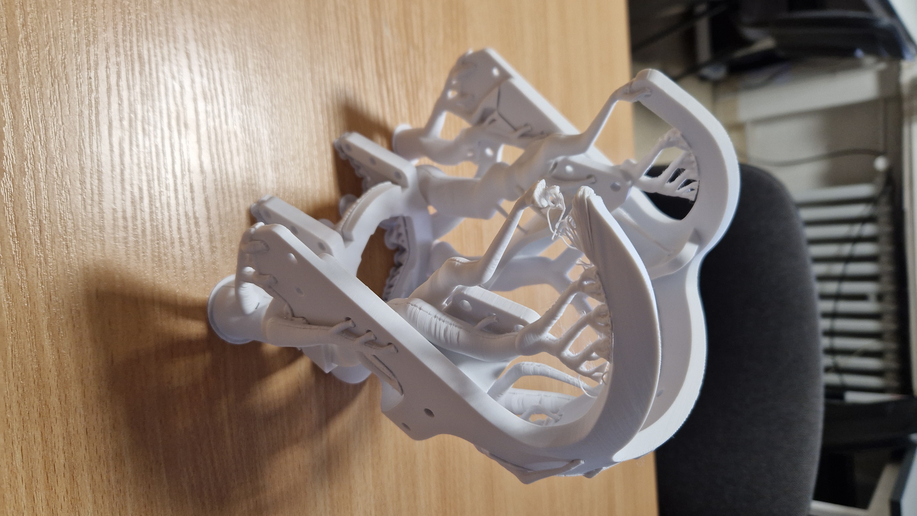
hardware-module/3Dmodel/Photos/failure2_2.jpg
